Matt-Santos/Cardless-Security-System/documents/images/Figures/Circuit_Schematic-4.png

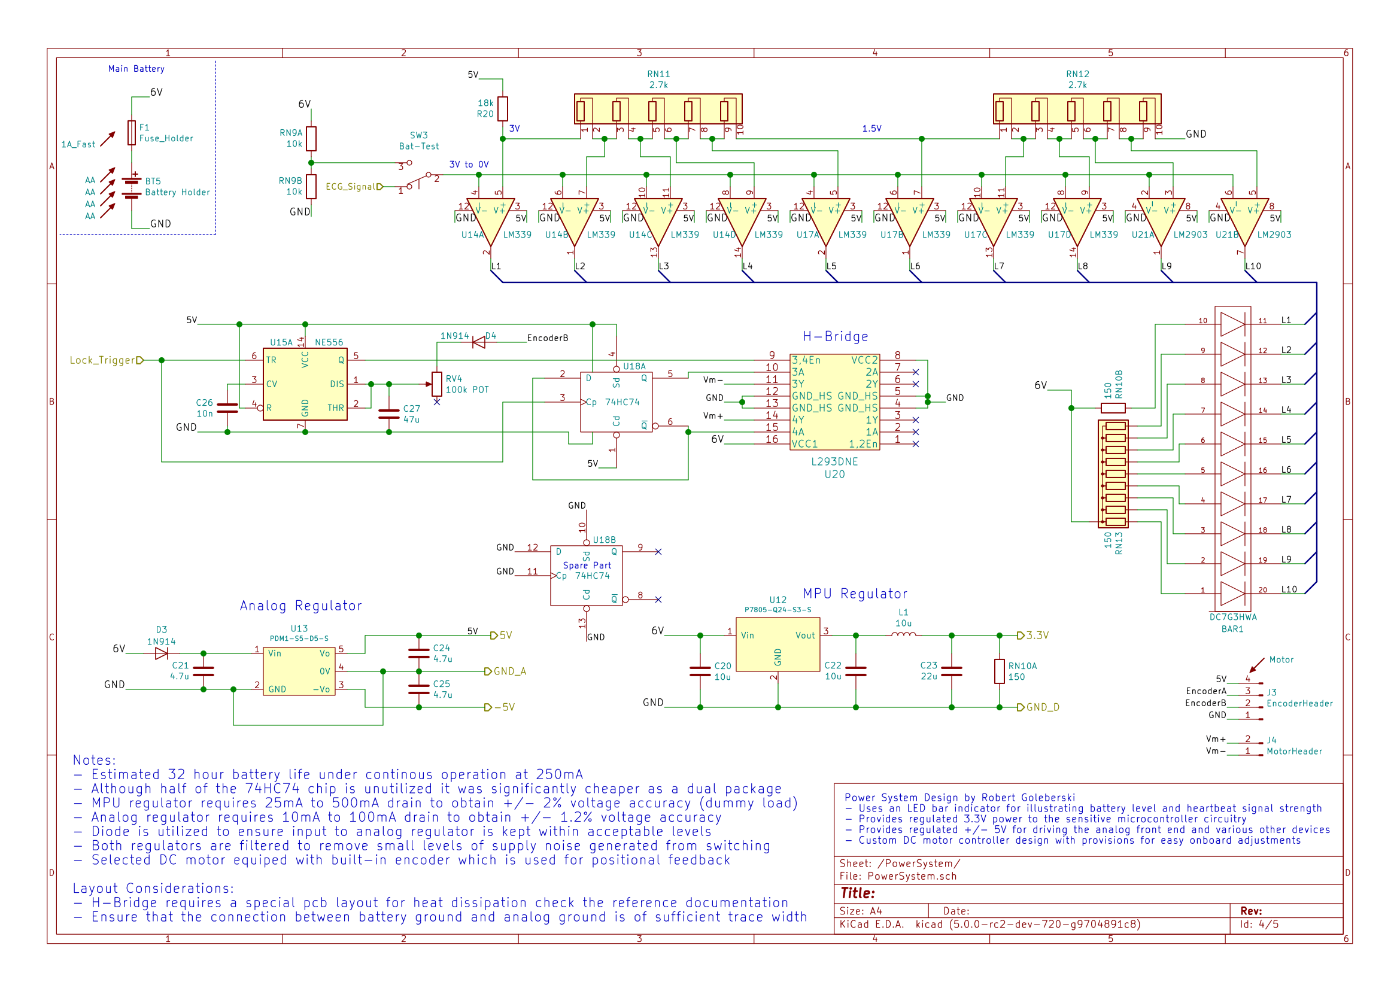
documents/images/Figures/Circuit_Schematic-4.png
