Matt-Santos/Cardless-Security-System/documents/images/gallery/Adding NetTies.jpg

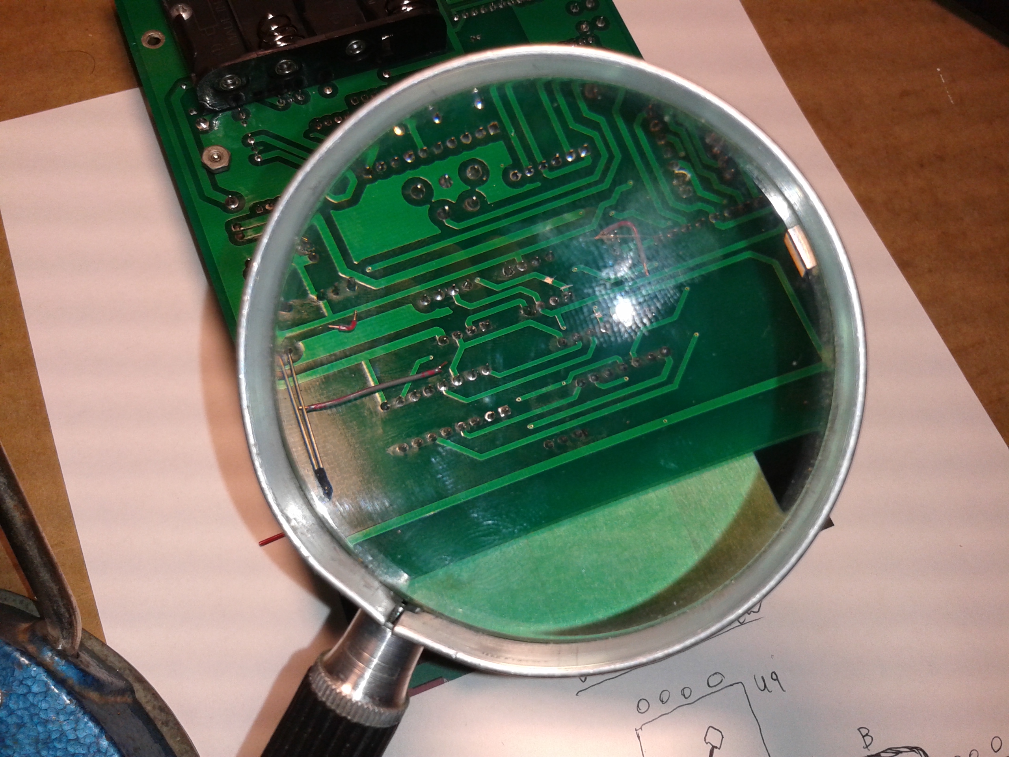
documents/images/gallery/Adding NetTies.jpg
