Matt-Santos/Cardless-Security-System/documents/images/gallery/Checking for Shorts.jpg

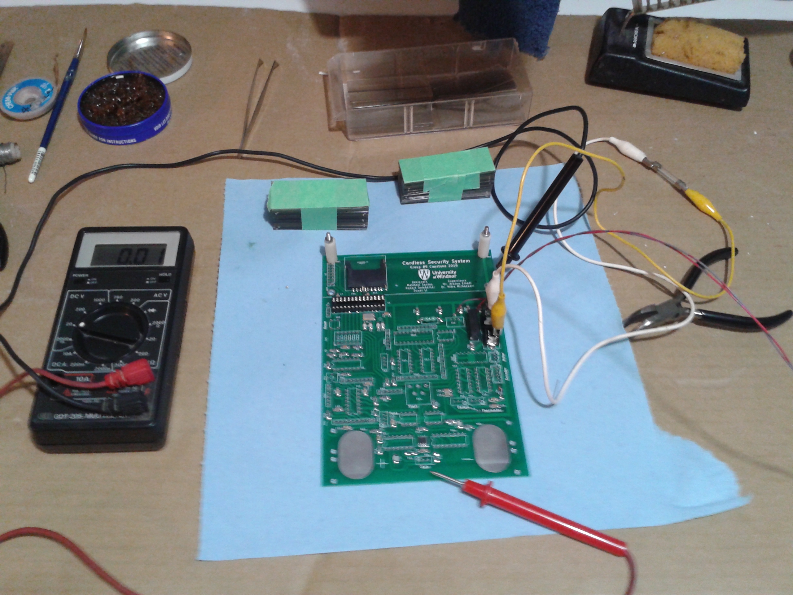
documents/images/gallery/Checking for Shorts.jpg
