Matt-Santos/Cardless-Security-System/documents/images/gallery/Finishing the Backside.jpg

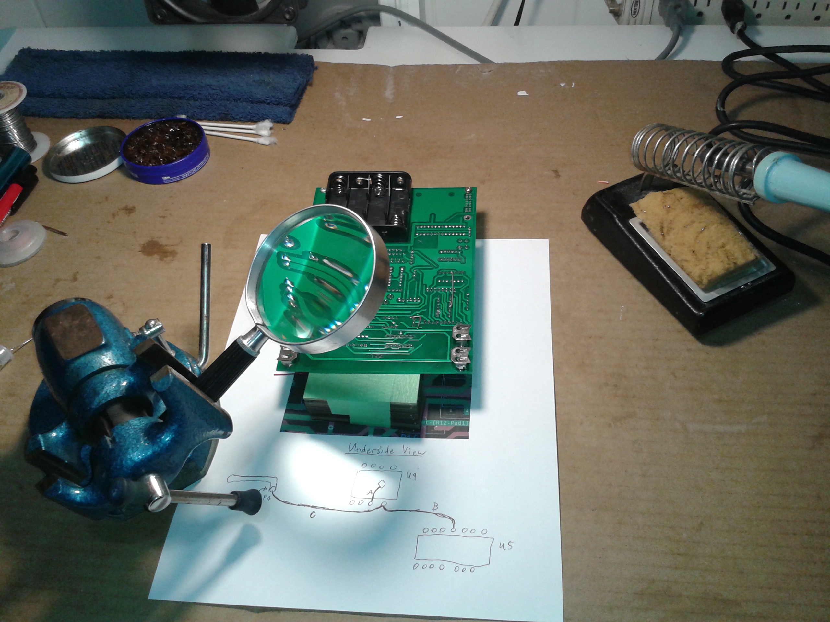
documents/images/gallery/Finishing the Backside.jpg
