Matt-Santos/Cardless-Security-System/documents/images/gallery/FirstChipRead.png

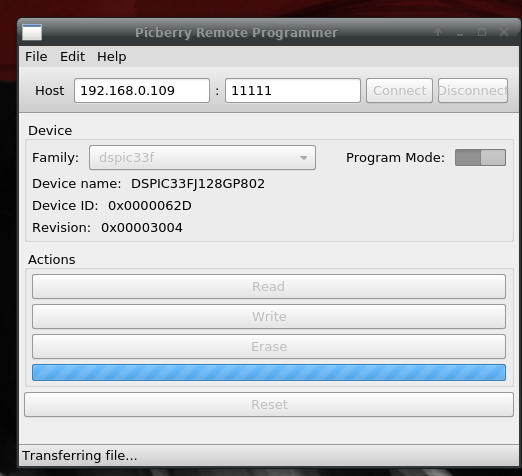
documents/images/gallery/FirstChipRead.png
