Matt-Santos/Cardless-Security-System/documents/images/gallery/Fscores.png

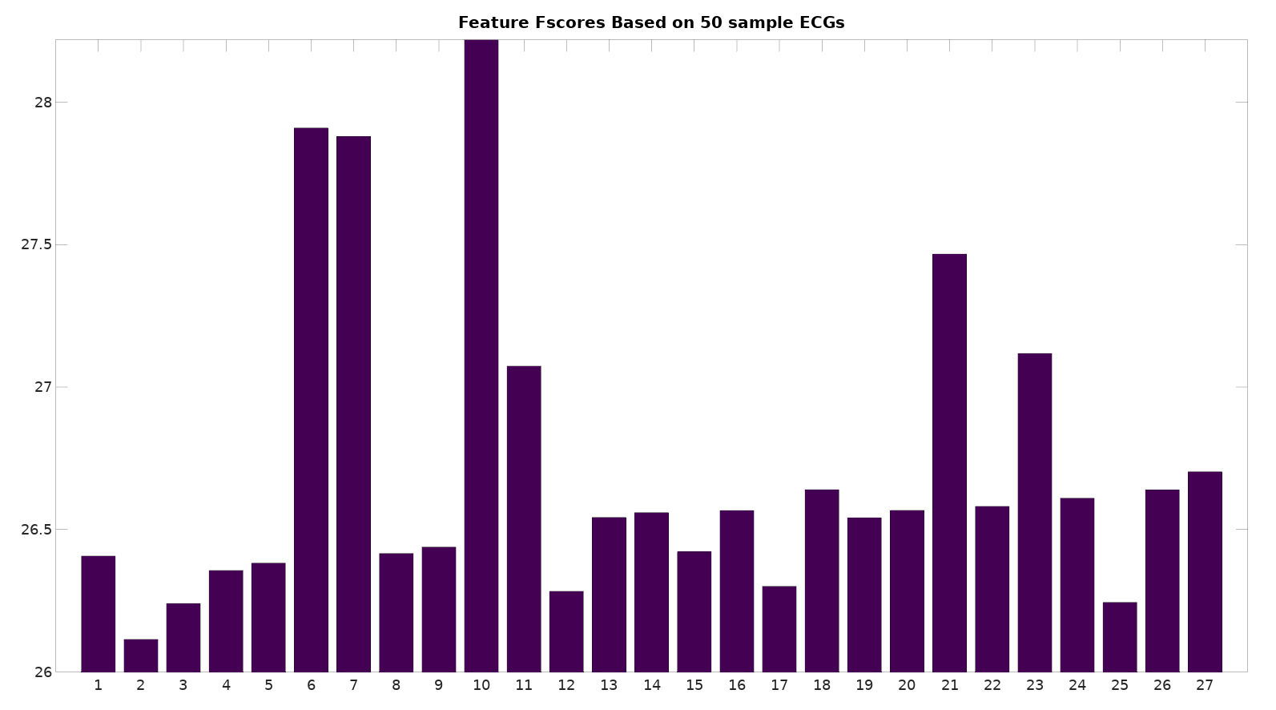
documents/images/gallery/Fscores.png
