Matt-Santos/Cardless-Security-System/documents/images/gallery/OLED Modifications.jpg

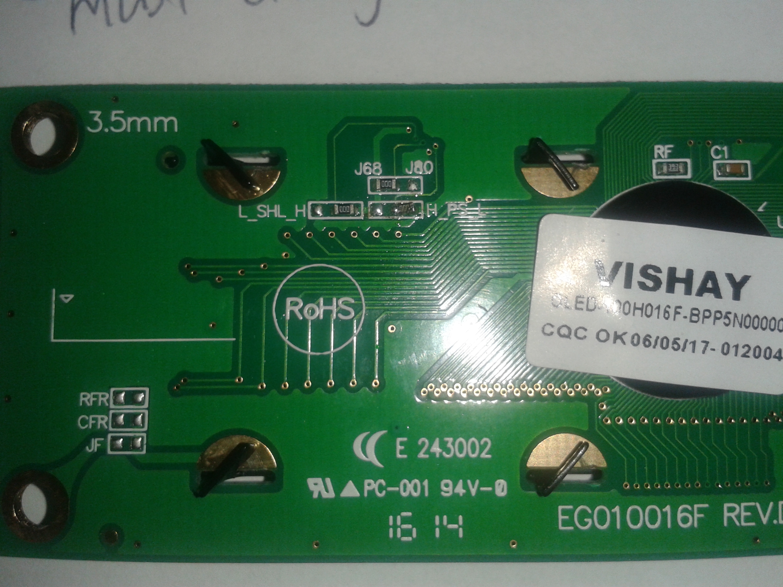
documents/images/gallery/OLED Modifications.jpg
