Matt-Santos/Cardless-Security-System/documents/images/gallery/Planning Stage.jpg

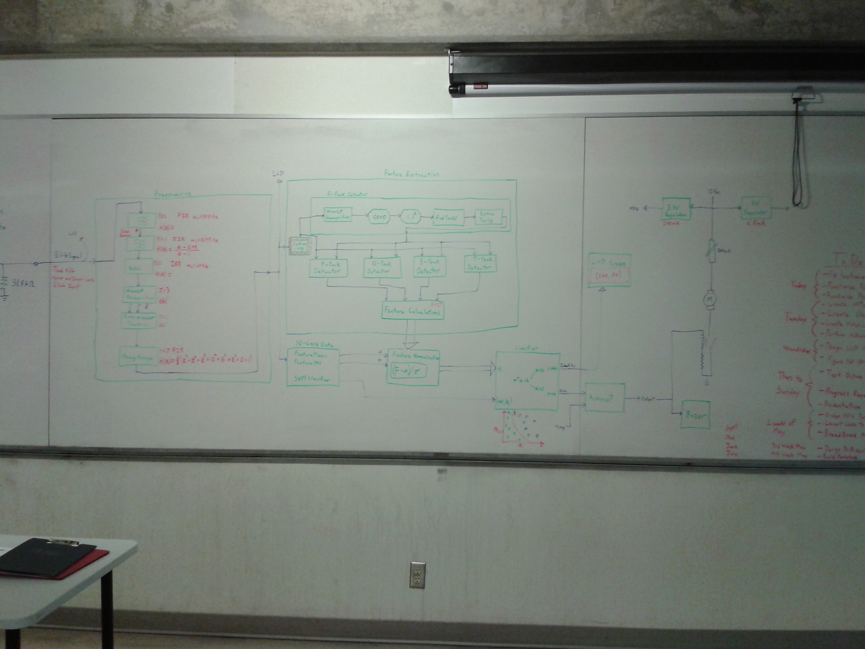
documents/images/gallery/Planning Stage.jpg
