Matt-Santos/Cardless-Security-System/documents/images/gallery/Reflow Process.jpg

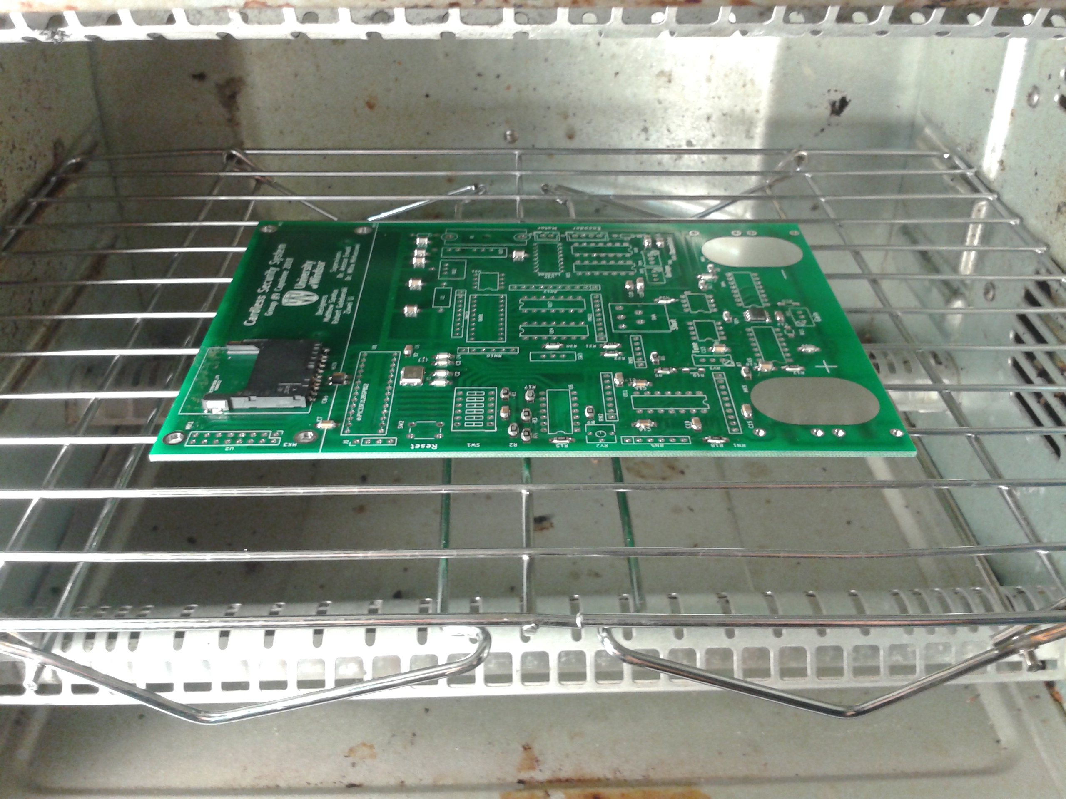
documents/images/gallery/Reflow Process.jpg
