Matt-Santos/Cardless-Security-System/documents/images/gallery/Trace Corrections.jpg

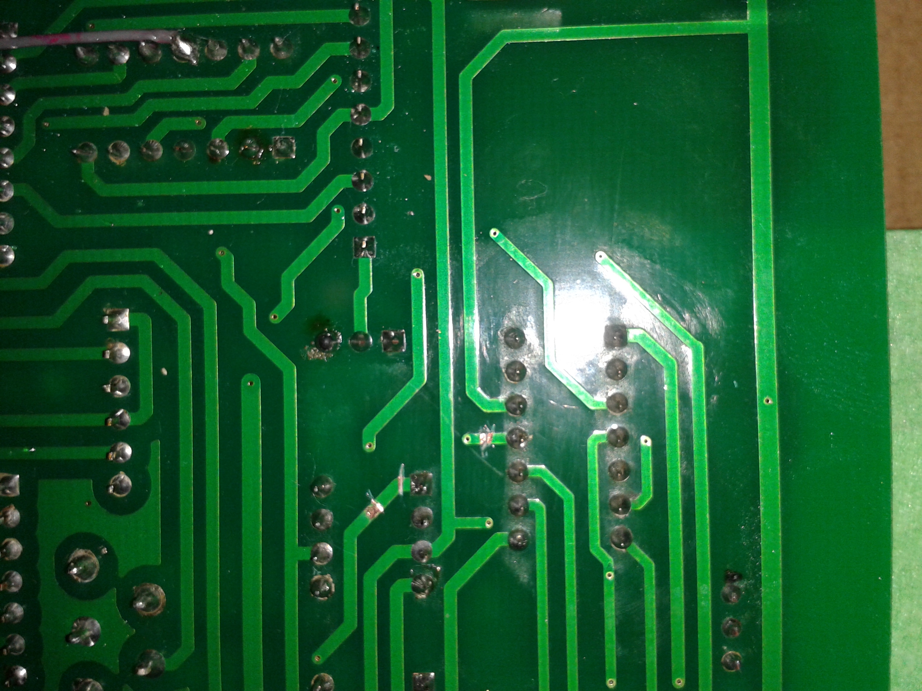
documents/images/gallery/Trace Corrections.jpg
