Matt-Santos/Cardless-Security-System/documents/images/gallery/Workstation.jpg

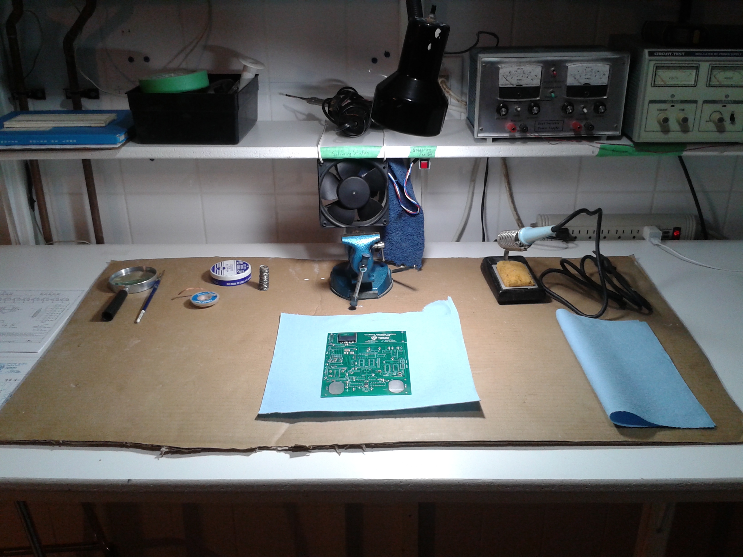
documents/images/gallery/Workstation.jpg
