Matt-Santos/Cardless-Security-System/documents/images/project.jpg

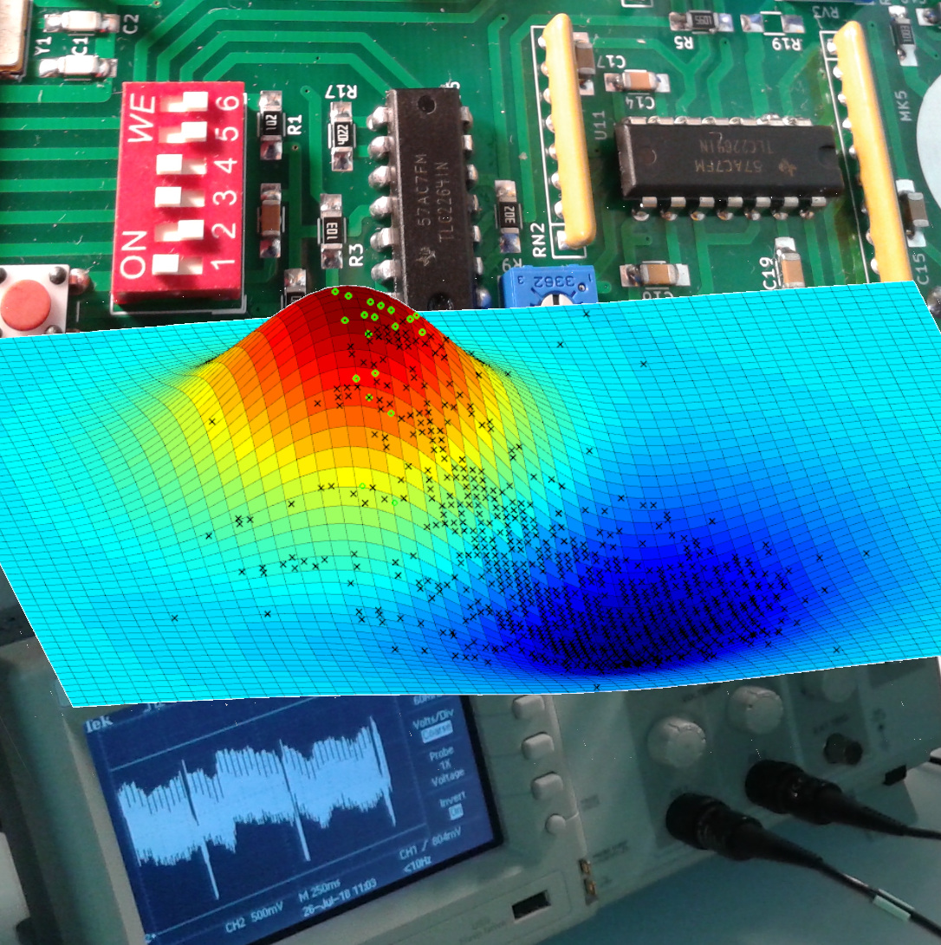
documents/images/project.jpg
