Matt-Santos/Cardless-Security-System/documents/images/gallery/Assembled Board Full View.jpg

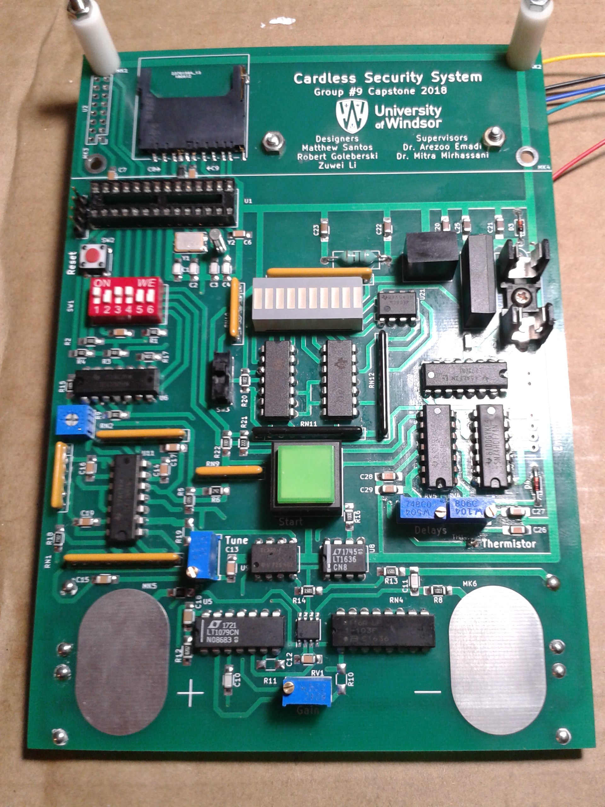
documents/images/gallery/Assembled Board Full View.jpg
