Matt-Santos/Cardless-Security-System/documents/images/gallery/Assembled Board.jpg

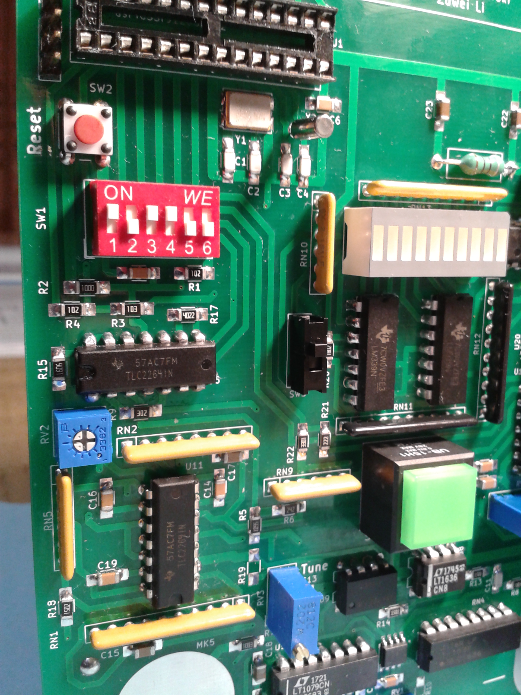
documents/images/gallery/Assembled Board.jpg
