Matt-Santos/Cardless-Security-System/documents/images/gallery/Harness Wiring.jpg

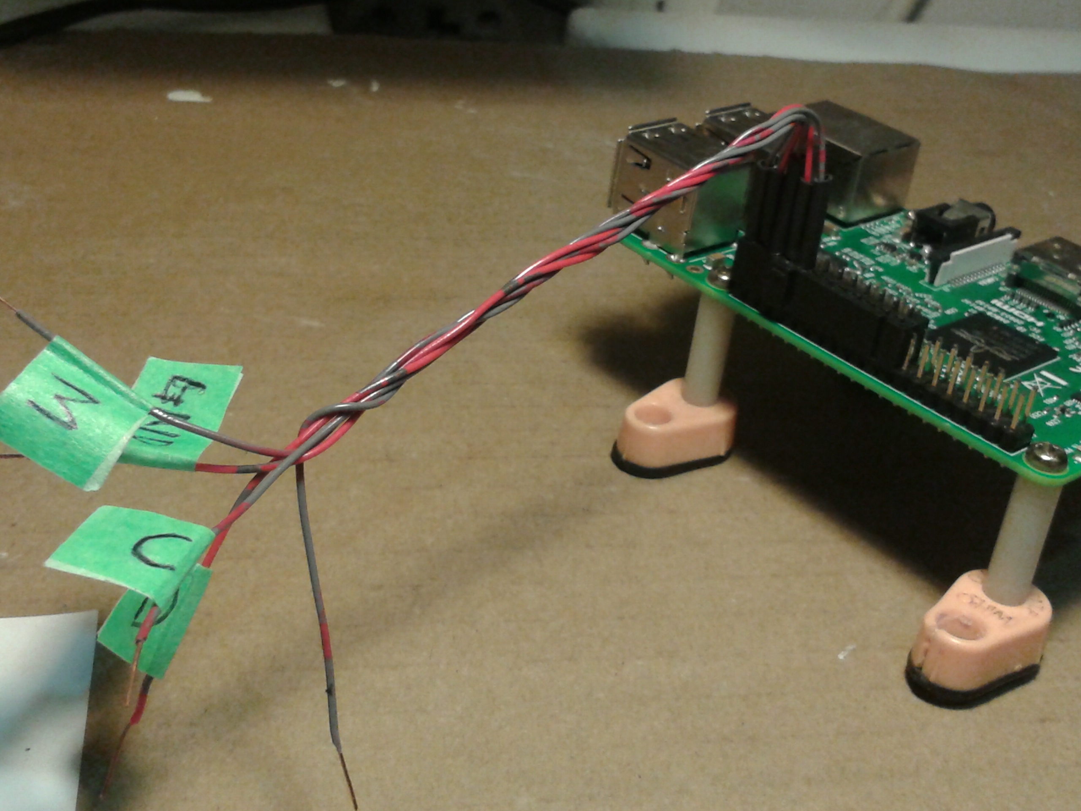
documents/images/gallery/Harness Wiring.jpg
