Matt-Santos/Cardless-Security-System/documents/images/gallery/Pre Solder Reflow.jpg

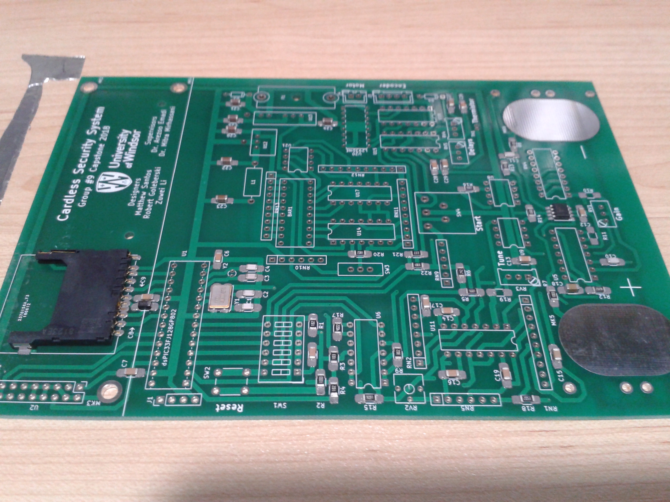
documents/images/gallery/Pre Solder Reflow.jpg
