Matt-Santos/Cardless-Security-System/documents/images/gallery/SMD Assembly.jpg

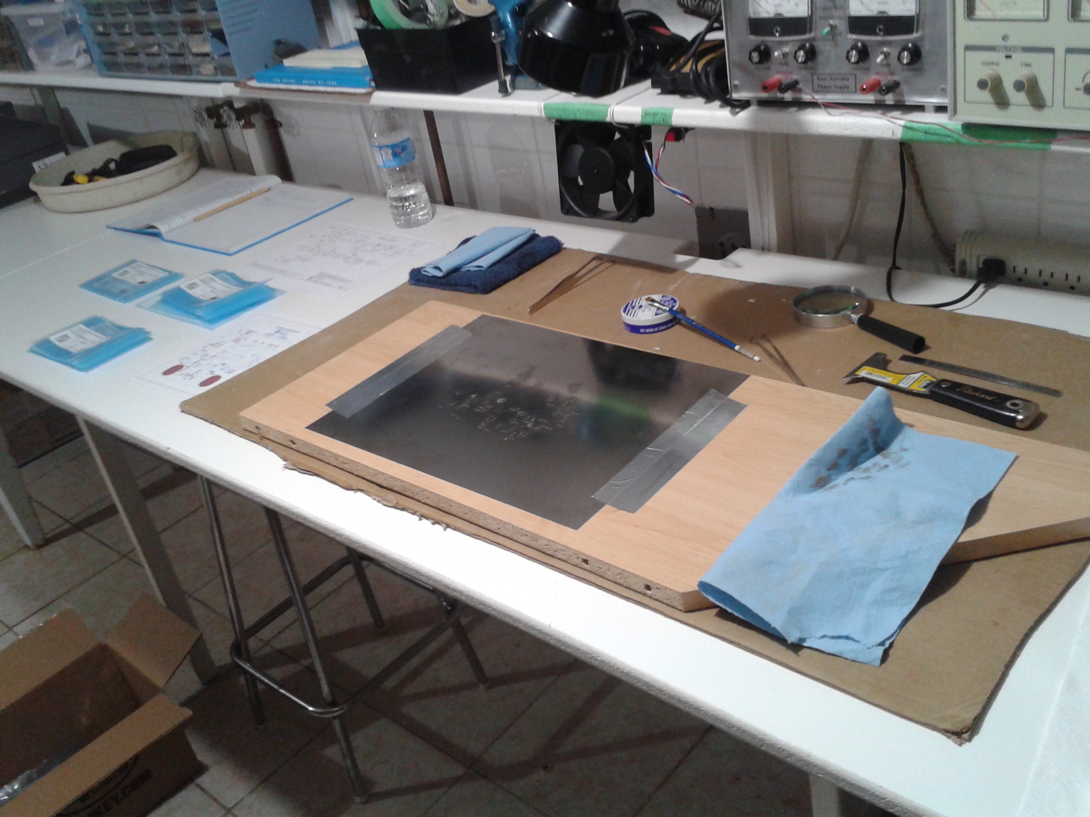
documents/images/gallery/SMD Assembly.jpg
