Matt-Santos/Cardless-Security-System/documents/images/gallery/OLED Testing.jpg

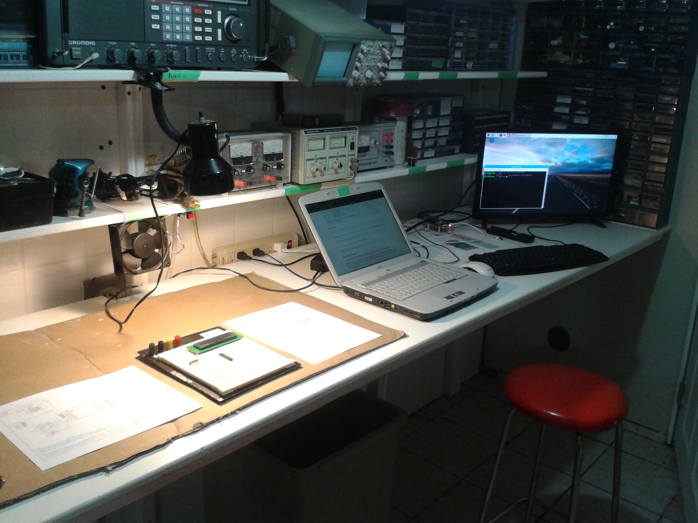
documents/images/gallery/OLED Testing.jpg
