Matt-Santos/Cardless-Security-System/documents/images/gallery/Prototype Test Circuit 2.jpg

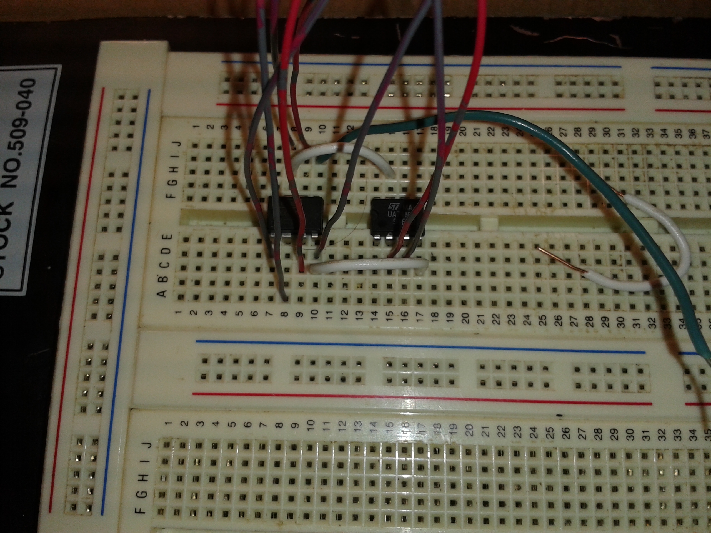
documents/images/gallery/Prototype Test Circuit 2.jpg
