Matt-Santos/Cardless-Security-System/documents/images/gallery/Prototype Test Circuit 3.jpg

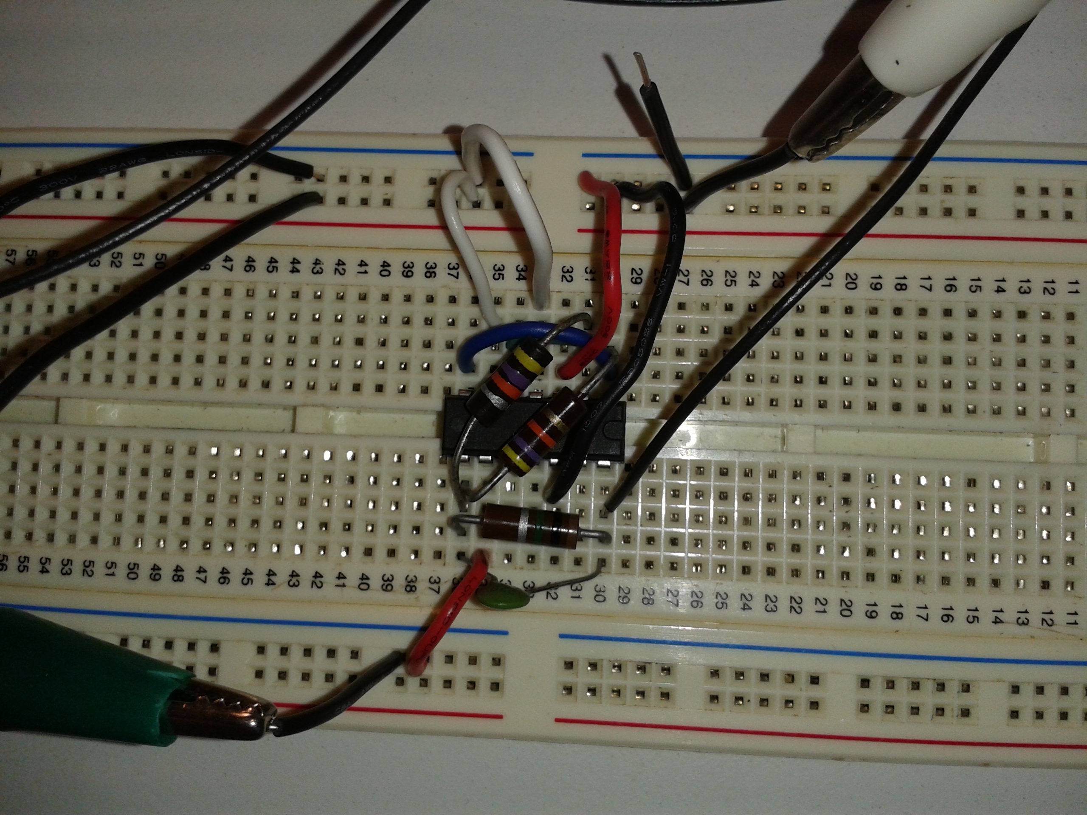
documents/images/gallery/Prototype Test Circuit 3.jpg
