Matt-Santos/Cardless-Security-System/documents/images/gallery/Prototype Test Circuit.jpg

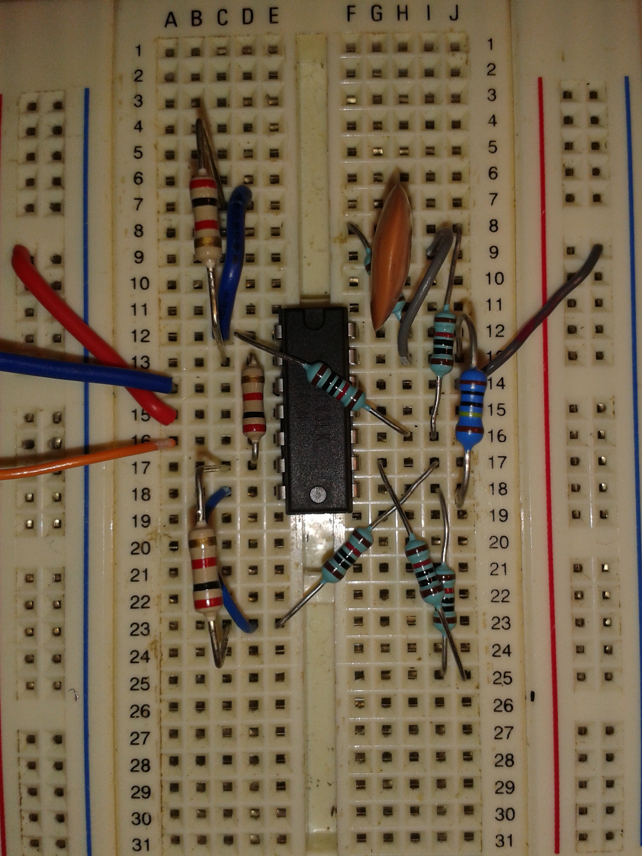
documents/images/gallery/Prototype Test Circuit.jpg
