Matt-Santos/Cardless-Security-System/documents/images/gallery/Prototype Testing.jpg

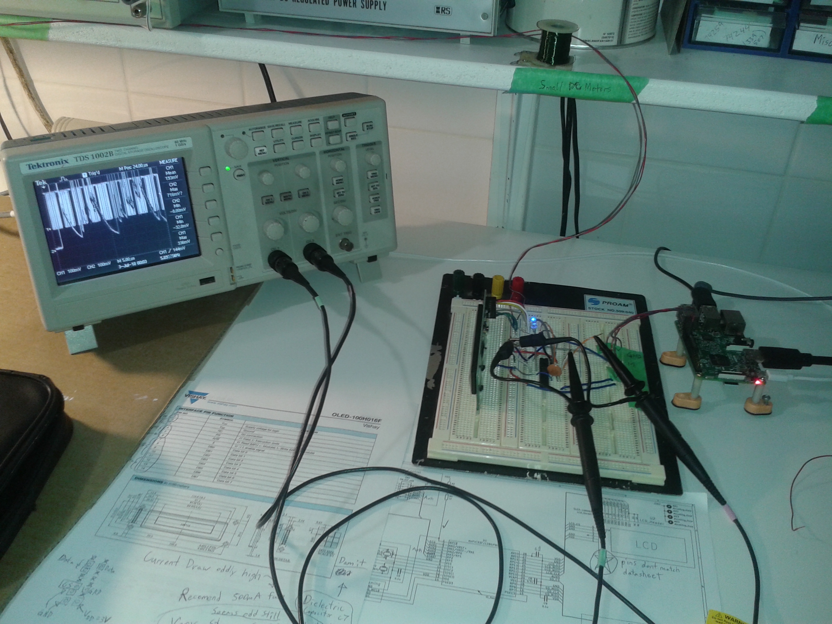
documents/images/gallery/Prototype Testing.jpg
