Matt-Santos/Cardless-Security-System/documents/images/Figures/Main-B.Cu.pdf

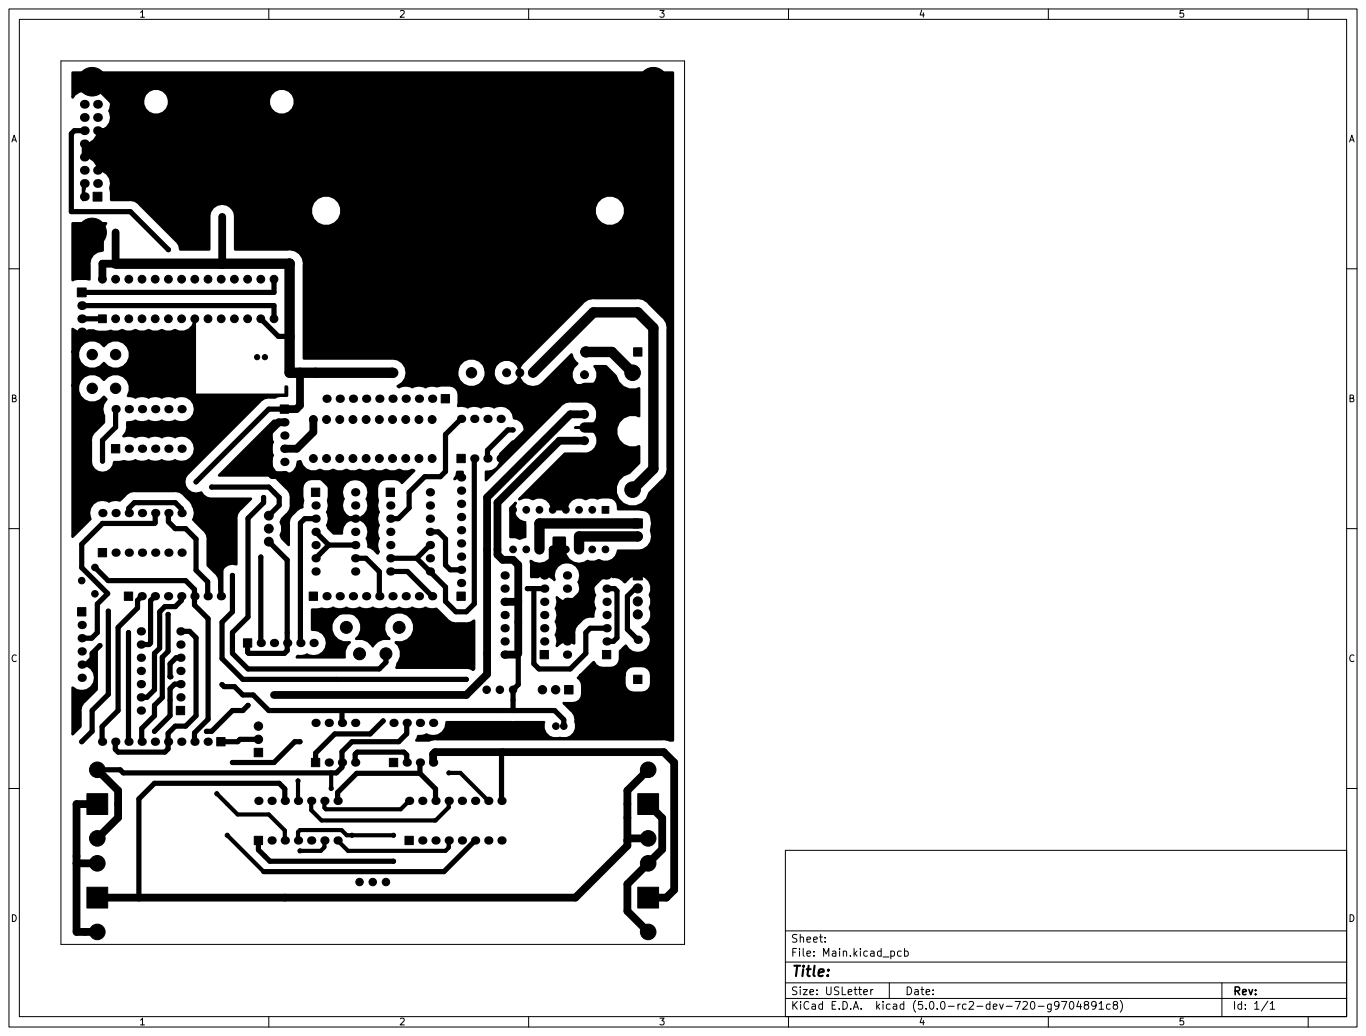
[picture p79: page 1]
