Matt-Santos/Cardless-Security-System/documents/images/Figures/Main-B.Mask.pdf

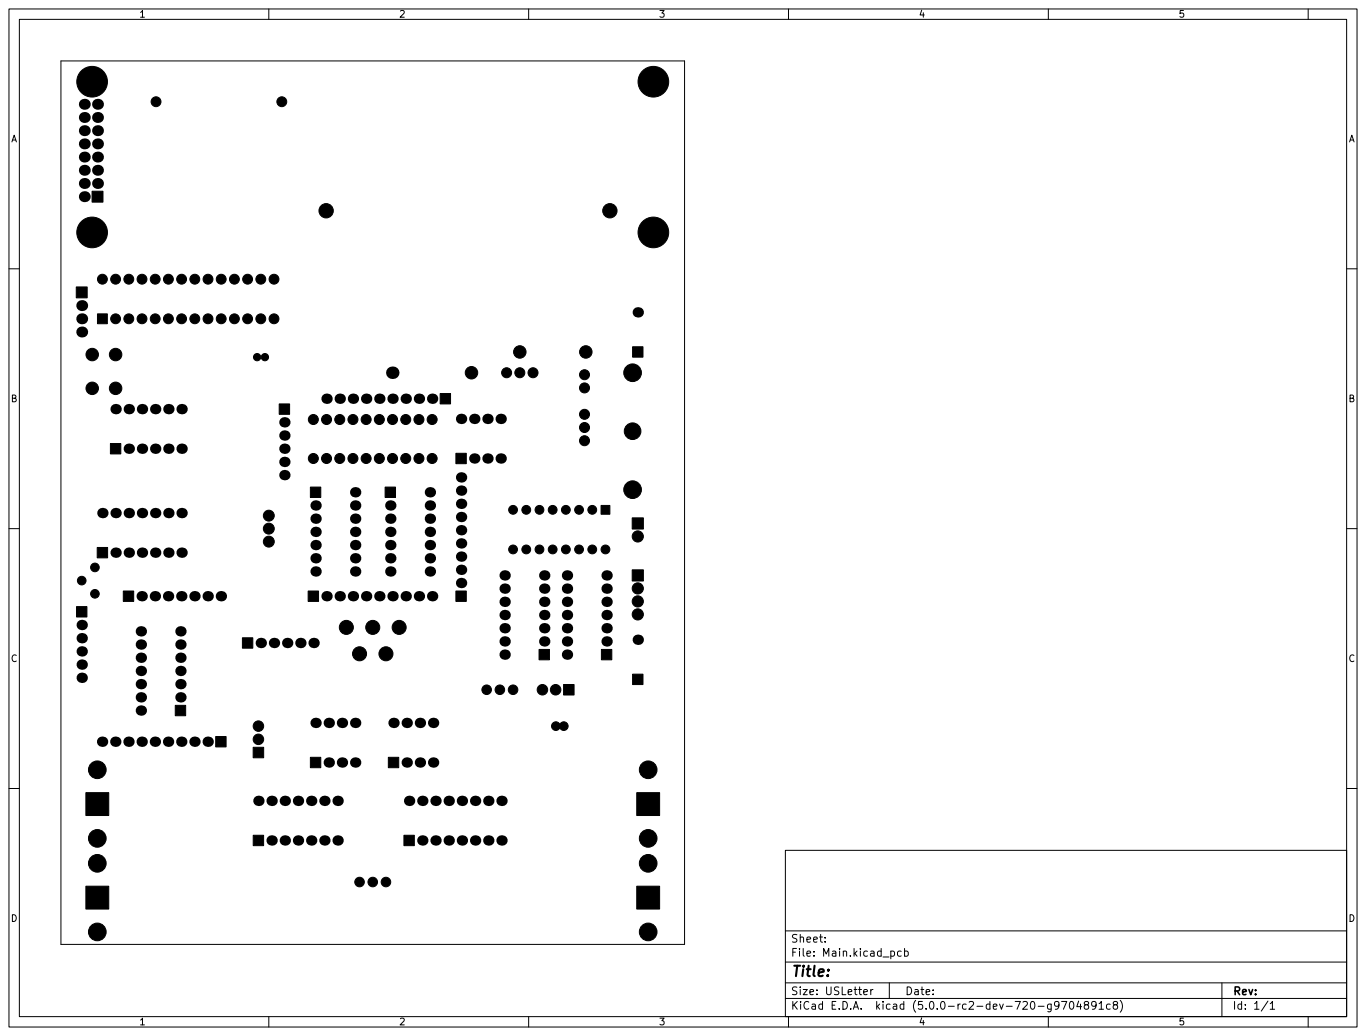
[picture p80: page 1]
