Matt-Santos/Cardless-Security-System/documents/images/Figures/Main-Edge.Cuts.pdf

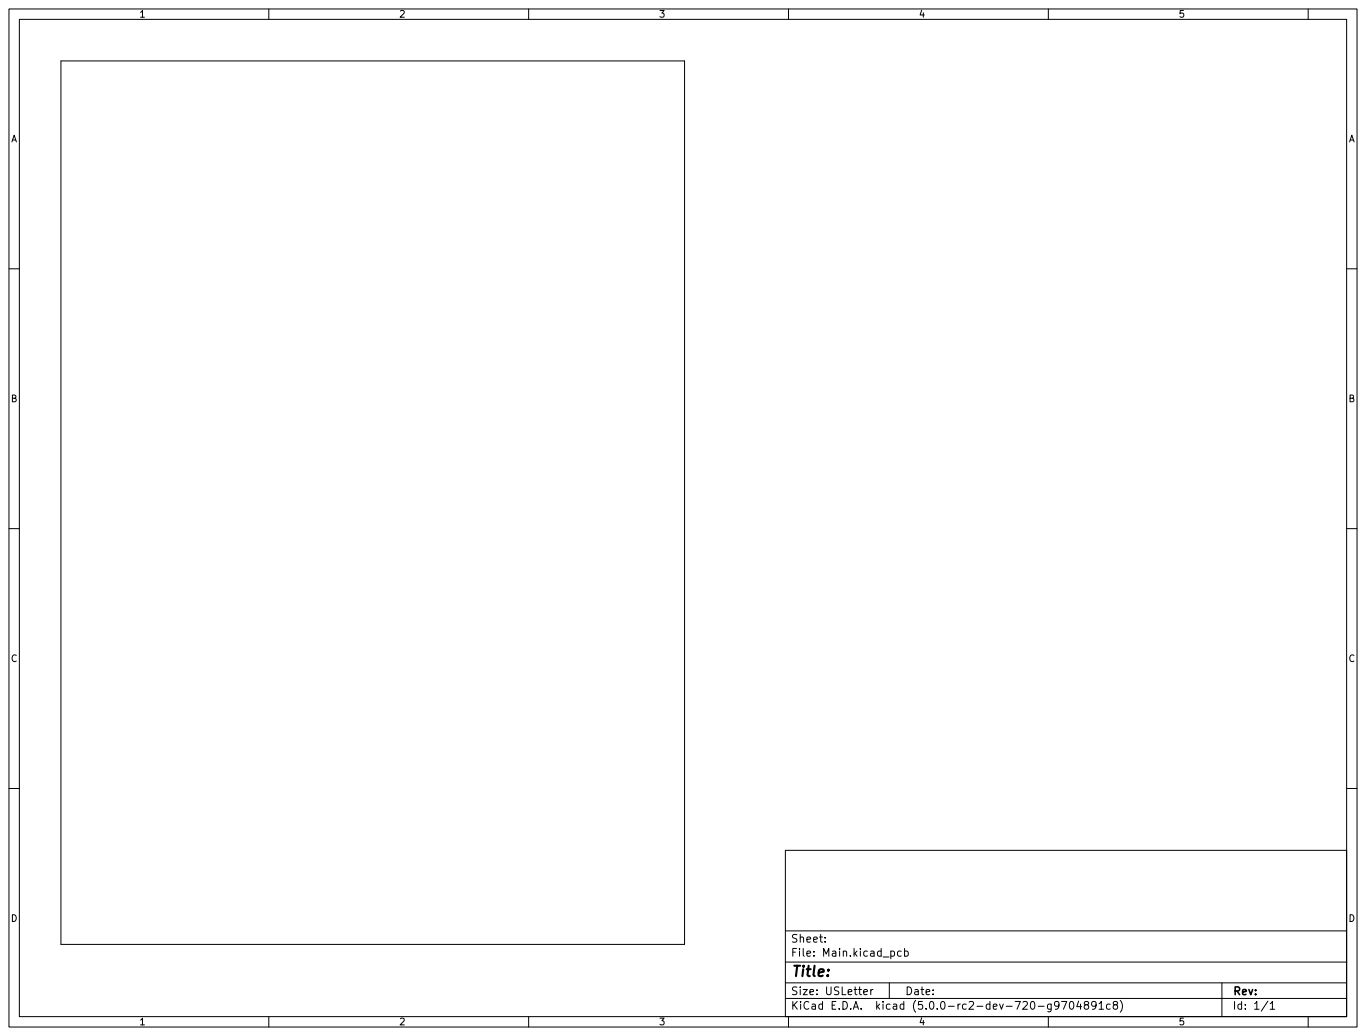
[picture p81: page 1]
