Matt-Santos/Cardless-Security-System/documents/images/Figures/Main-F.Cu.pdf

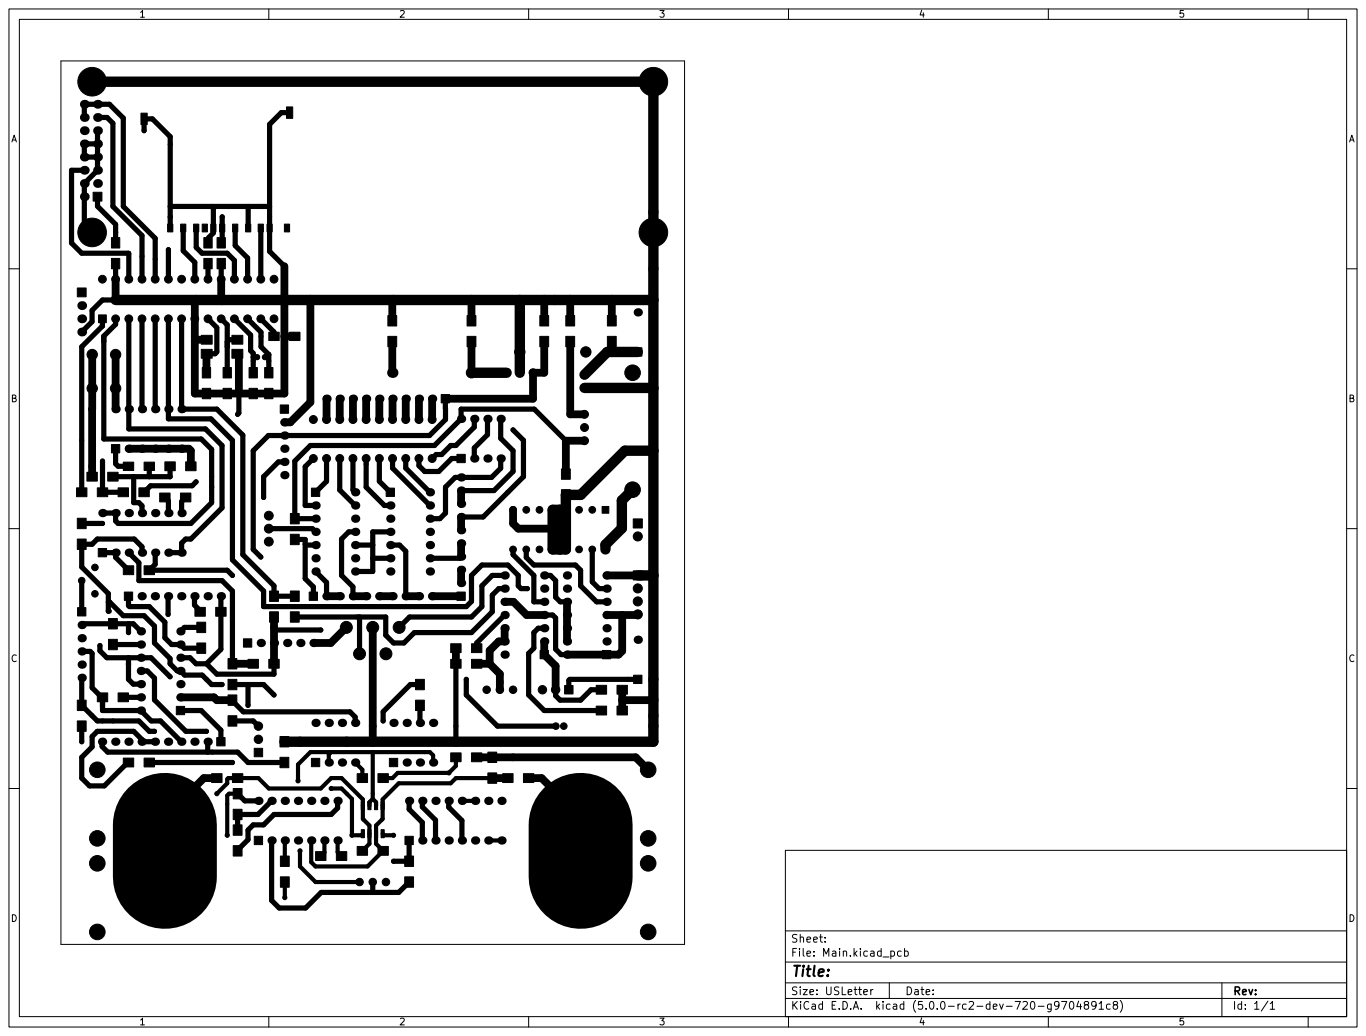
[picture p82: page 1]
