Matt-Santos/Cardless-Security-System/documents/images/Figures/Main-F.Mask.pdf

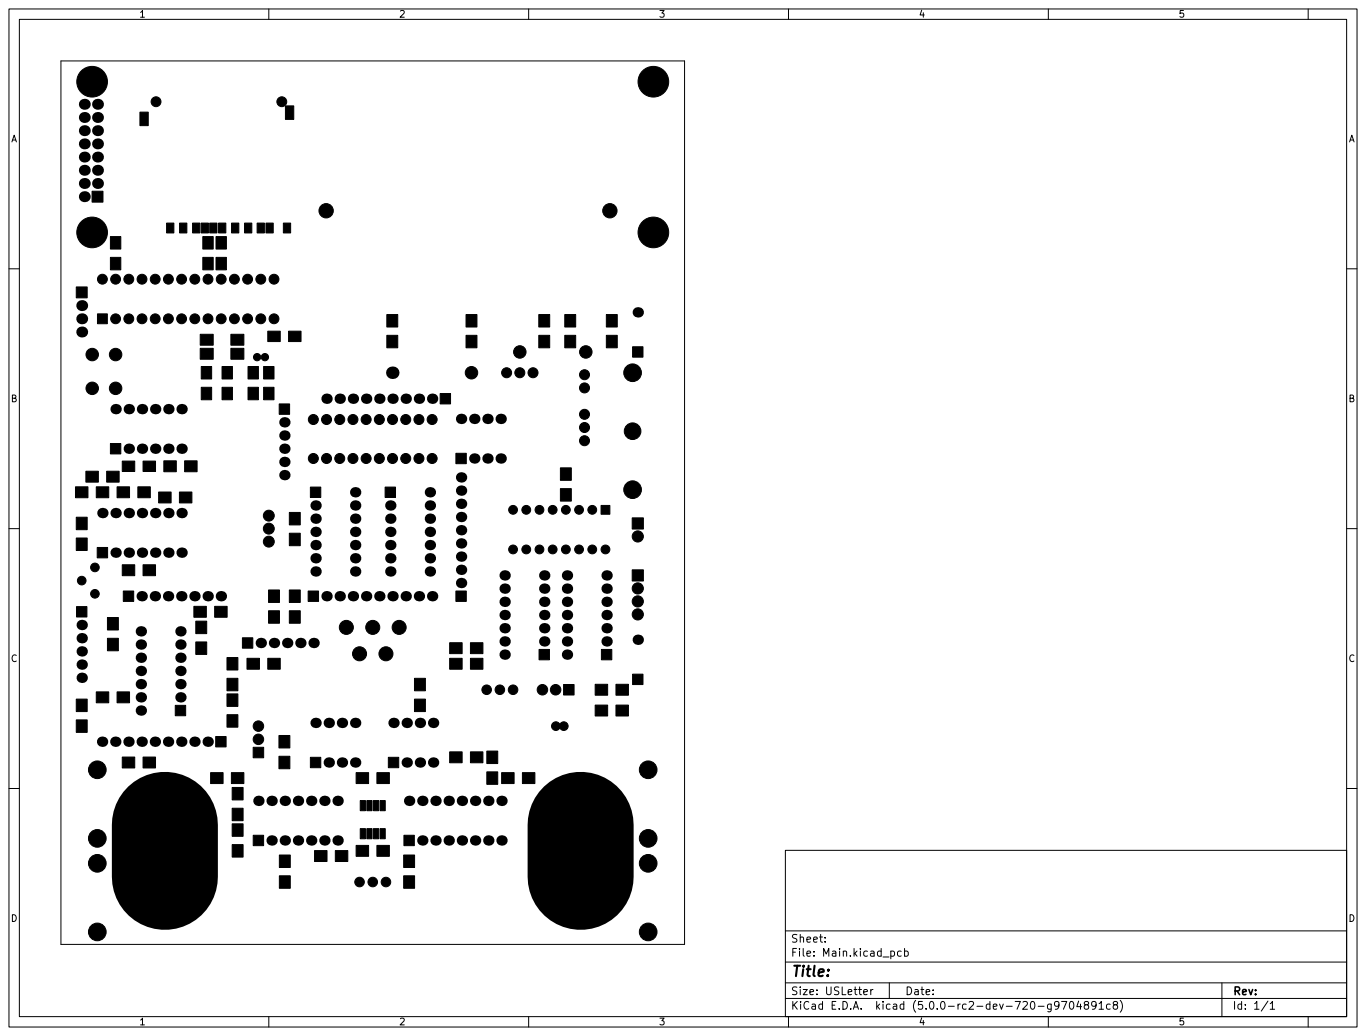
[picture p83: page 1]
