Matt-Santos/Cardless-Security-System/documents/images/Figures/Main-F.SilkS.pdf

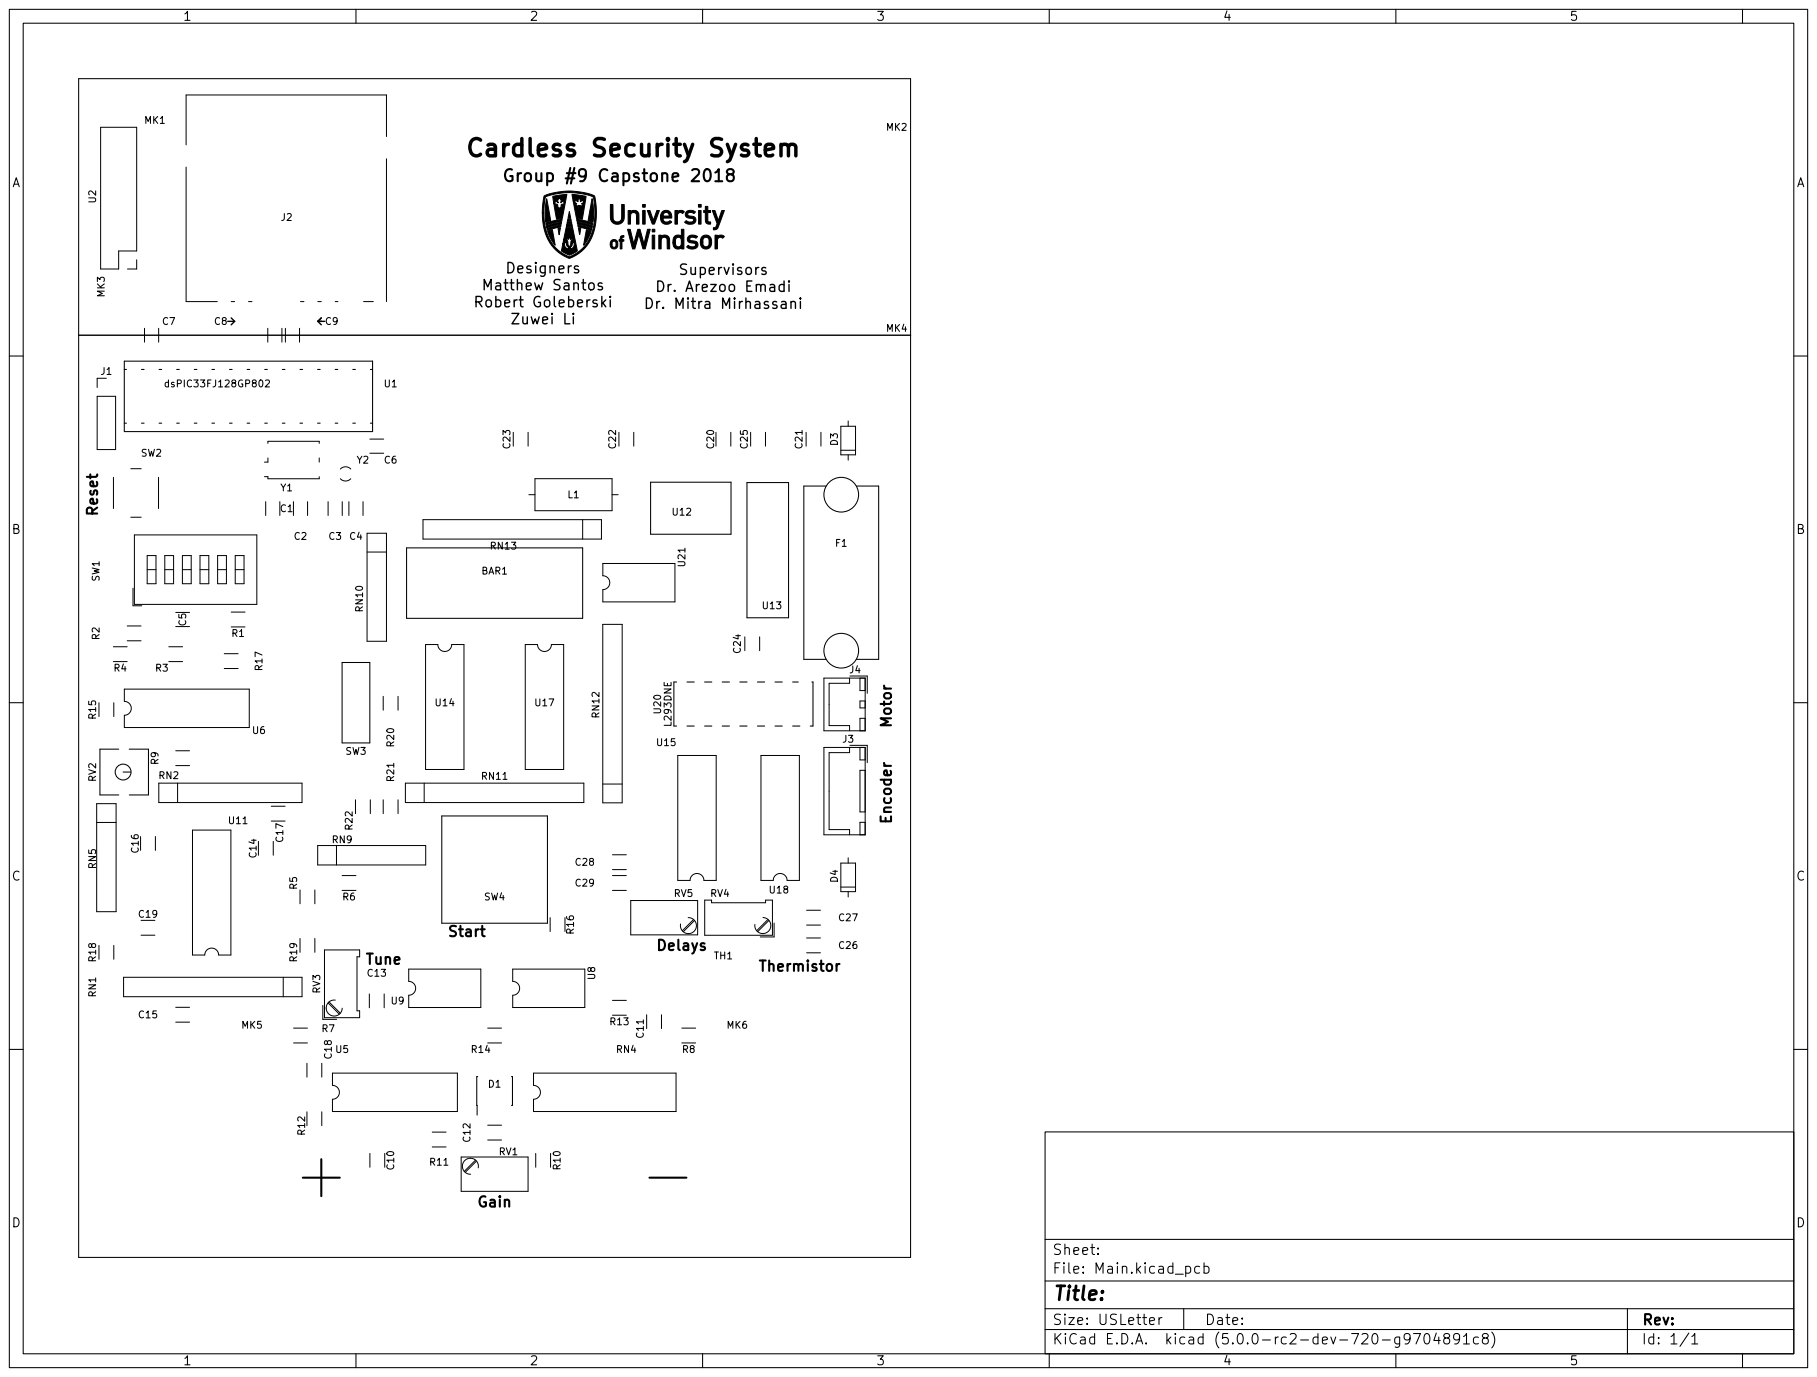
[picture p84: page 1]

Cardless Security System
Supervisors Dr. Arezoo Emadi Dr. Mitra Mirhassani Group #9 Capstone 2018
