Matt-Santos/Cardless-Security-System/hardware/LTSpice Simulations/ECG_Front/FrontEnd.asc

B1: bv; V=white(1e4*time)*{CM_Noise}
C1: cap; {mc(1n,0.1)}
C2: cap; {mc(100p,0.1)}
C3: cap; {mc(100p,0.1)}
C4: cap; 438.2µ
C5: cap; 27.5µ
C6: cap; 438.2µ
C7: cap; 27.5µ
C8: cap; {mc(47u,0.1)}
C9: cap; 9
C10: cap; {mc(680n,0.1)}
C11: cap; {mc(68n,0.1)}
C12: cap; {mc(680n,0.1)}
C13: cap; {mc(68n,0.1)}
C14: cap; {mc(680n,0.1)}
C15: cap; {mc(68n,0.1)}
D1: diode
D2: diode
D3: diode
D4: diode
R1: res; 500
R2: res; {mc(2k,0.01)}
R3: res; {mc(2k,0.01)}
R4: res; {mc(100k,0.01)}
R5: res; {mc(100k,0.01)}
R6: res; {mc(10k,0.01)}
R7: res; {mc(10k,0.01)}
R8: res; {mc(20k,0.01)}
R9: res; {mc(20k,0.01)}
R10: res; 3.5k
R11: res; 121.9k
R12: res; 172k
R13: res; 3.5k
R14: res; 121.9k
R15: res; 172k
R16: res; 9k
R17: res; {mc(1.5k,0.01)}
R18: res; 1k
R19: res; {mc(20k,0.01)}
R20: res; 9Meg
R21: res; {mc(100,0.1)}
R22: res; {mc(1.5k,0.01)}
R23: res; {mc(1k,0.01)}
R24: res; {mc(2k,0.01)}
R25: res; {mc(82k,0.1)}
R26: res; {mc(15k,0.01)}
R27: res; {mc(10k,0.1)}
R28: res; {mc(10k,0.1)}
R29: res; {mc(3.6k,0.1)}
R30: res; {mc(3.6k,0.1)}
R31: res; {mc(3.6k,0.1)}
R32: res; {mc(3.6k,0.1)}
R33: res; {mc(10k,0.1)}
R34: res; {mc(3.6k,0.1)}
R35: res; 1.5k
R36: res; 1k
R38: res; {mc(1k,0.1)}
R39: res; 40k
R40: res; 10k
U1: IL300
U2: OP747
U3: OP747
U4: LT1079
U5: LT1079
U6: LT1079
U7: LT1079
U8: OP747
U9: OP747
U10: OP727
U11: OP777
U12: OP727
V1: voltage; SINE(0 {Signal/2} 10); AC {Signal/2}
V2: voltage; SINE(0 {Signal/2} 10); AC {Signal/2}
V3: voltage; {CM_Bias}
V4: voltage; 3; Rser=1
V5: voltage; 3; Rser=1
V6: voltage; SINE(0 {Drift/2} 0.5)
V7: voltage; SINE(0 {Drift/2} 0.5)
V8: voltage; SINE(0 {EMI/2} 60)
V9: voltage; SINE(0 {EMI/2} 60)
V10: voltage; 5; Rser=1
V11: voltage; 5; Rser=1
V12: voltage; {DC_Bias/2}
V13: voltage; {DC_Bias/2}
Named nets: Vee, Vcc, 0, Ve, Vc, FGND, Vp, Vn
.tran 0.05
;ac dec 10 0.01 5000
;noise V(Out) V(Noise) dec 10 0.01 1000
-Inrush Current protection
-Voltage Clamping
-Preliminary Passive Lowpass Filter
CM DC
  Bias
CM Noise
Differential Input Signal
BaselineDrift
Approximate Human ECG Signal Model
Human Finger Impedance
(Burke and Molloy)
Pre-Amplifier (Instrumental)
60Hz EMI
Cell Battery Supply
Circuit Protection and Noise Filtering
;step param run 1 50 1
Main Supply
Link to Floating GND
(For Simulation Only)
Bipolar Optoisolatior
Min   Output is +/- 50mV
Ideal Output is +/- 100mV
Max  Output is +/- 200mV
Otherwise Isolator will Saturate
- gain control from G=3.6 to 82 useable from 4 to18 which is 500 to 3.8k on the POT
- avoid right leg drive by using DC coupled refrence feedback via Integrator
- uses precise low noise opamps designed for low frequency operation
- IL300-F-X009 has best linearity of +/- 0.5% between 1mA and 10mA and max IF of 60mA
- IF was tuned to center of 10mA +/- 5mA per 100mV input (headroom to 200mA at 20mA before saturation)
- K3 has a tolerance range from 0.945 to 1.061 so a small 2k pot was added to allow fine tuning for unity gain
2k Tunning POT
DC Bias
BaselineDrift
60Hz EMI
DC Bias
.param CM_Bias=0.1 CM_Noise=0 DC_Bias=100m Signal=1m Drift=0m EMI=10m
G1=1.8 to 41
G2=2
5k POT
G = 1 = -R30/R31
fc = 120Hz = 1/(2pi*R30*R27&C10*C11)
Uses Multiple Feedback Filters as they are more robust to component tollerances and cascade better than sallenkey
Gain Control POT on the last stage allows for calibrating the input amplitude to the ADC and gives range from G= 0.8  to 1.8
Filters have a Quality of about 0.8 which gives reasonably sharp fall off as desired
Filter Network
Human Finger ECG Examination:
- able to resolve ECG on scope, typically about 1mV but seriously distorted by EMI noise
- EMI noise levels are on the order of 5mV normally and were shown to rise to 10mV with arm wrapped in hairdrier
- Differential DC Bias (aka Baseline Drift) levels were on the order of about 50mV normally with jumps to 100mV under movement
3k Gain Control POT
.param CM_Bias=0.1 CM_Noise=1 DC_Bias=100m Signal=1m Drift=2m EMI=10m
2nd Order Low Pass
2nd Order Low Pass
2nd Order Low Pass
ISSUE?
RRO but not at 3V???
Why is the buffer having this problem?
G=4.5
DC Injection
Uses a non-inverting summing opamp configuration
