Matt-Santos/Cardless-Security-System/hardware/LTSpice Simulations/TempSensor/Temperature.asc

R1: res; 2500
R2: res; 3k
R3: res; 5.6k
R4: res; 13k
U10: OP727
U12: OP727
V10: voltage; 5; Rser=1
V11: voltage; 5; Rser=1
Named nets: 0, Ve, Vc
.tran 0.05
Main Supply
Simple and makes full use of the NTC's Linear Range
See Excel "Beta Calculator" for NTC Details and Rational
